Cath272/MiniLatte/lucrare licenta/images/back-3.3v-rail.png

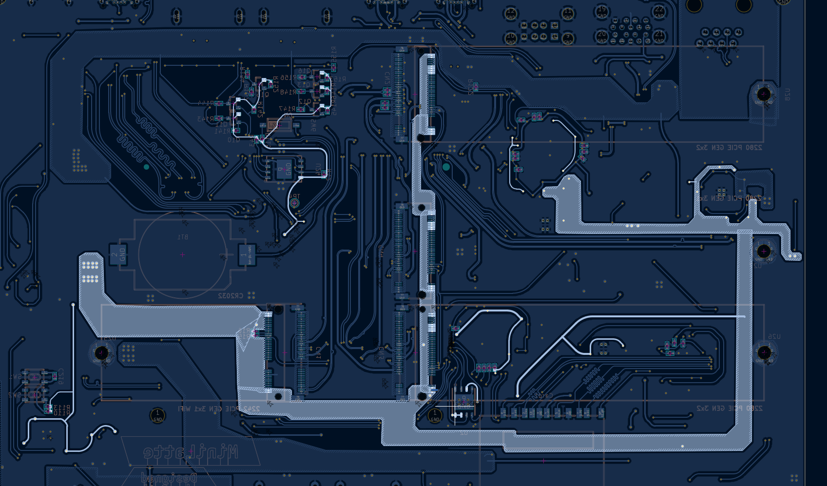
lucrare licenta/images/back-3.3v-rail.png
