Cath272/MiniLatte/lucrare licenta/images/LattePanda Mu.png

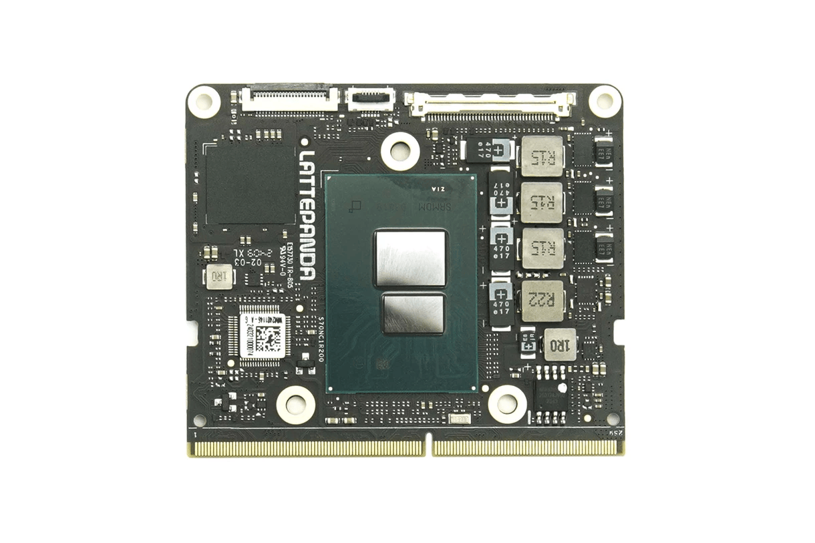
lucrare licenta/images/LattePanda Mu.png
