Cath272/MiniLatte/lucrare licenta/images/MiniLatte.png

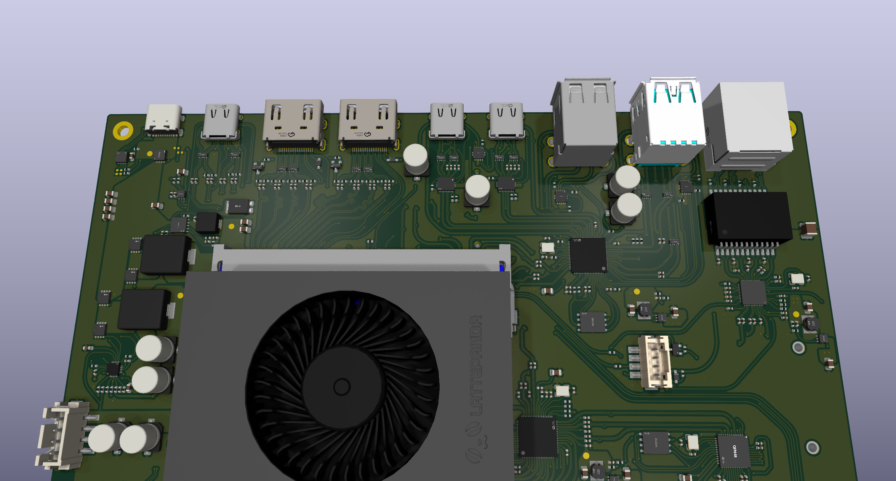
lucrare licenta/images/MiniLatte.png
