Cath272/MiniLatte/lucrare licenta/images/pcb-top-back.jpg

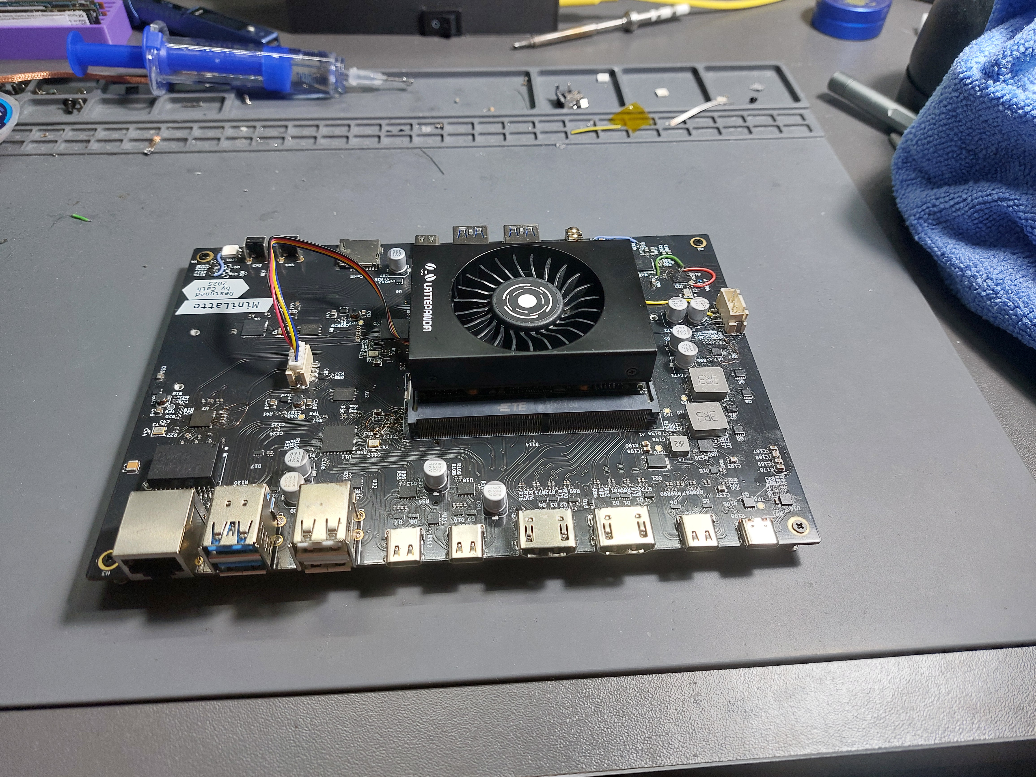
lucrare licenta/images/pcb-top-back.jpg
