Cath272/MiniLatte/pictures/WhatsApp Image 2025-12-02 at 20.27.55_821a572c.jpg

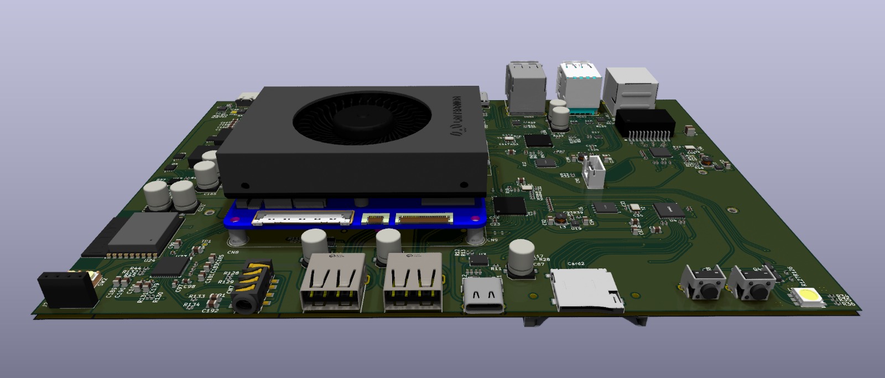
pictures/WhatsApp Image 2025-12-02 at 20.27.55_821a572c.jpg
