Cath272/MiniLatte/pictures/WhatsApp Image 2025-12-02 at 20.27.55_9503f0b6.jpg

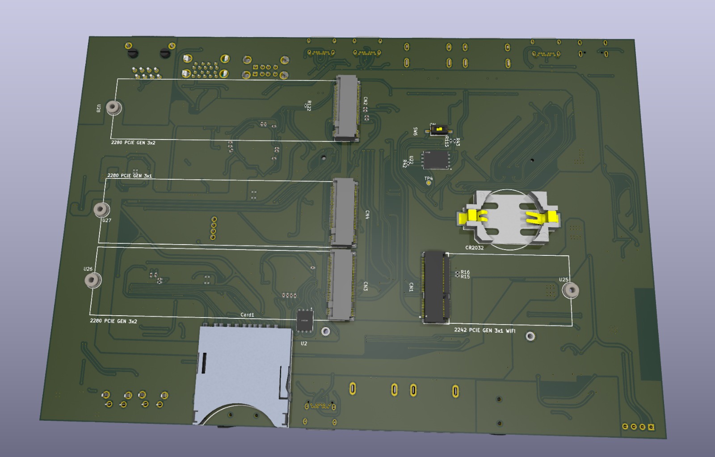
pictures/WhatsApp Image 2025-12-02 at 20.27.55_9503f0b6.jpg
