Cath272/MiniLatte/pictures/WhatsApp Image 2025-12-02 at 20.27.55_efc75e89.jpg

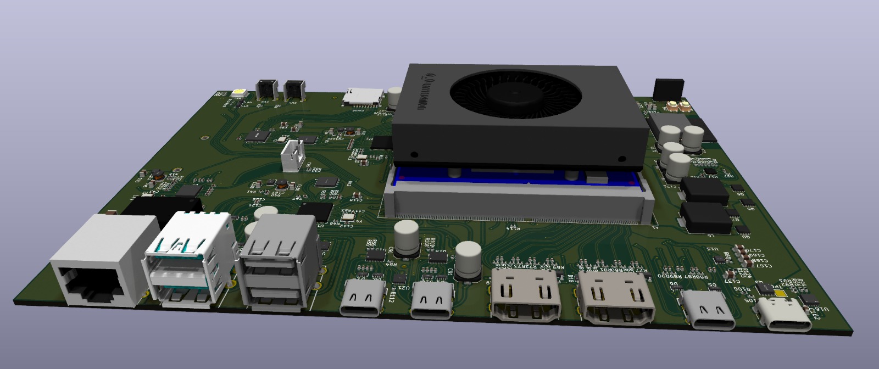
pictures/WhatsApp Image 2025-12-02 at 20.27.55_efc75e89.jpg
